switux/AstroWeatherStation/pictures/SQM + CloudCover sensors _1 of 2.JPG

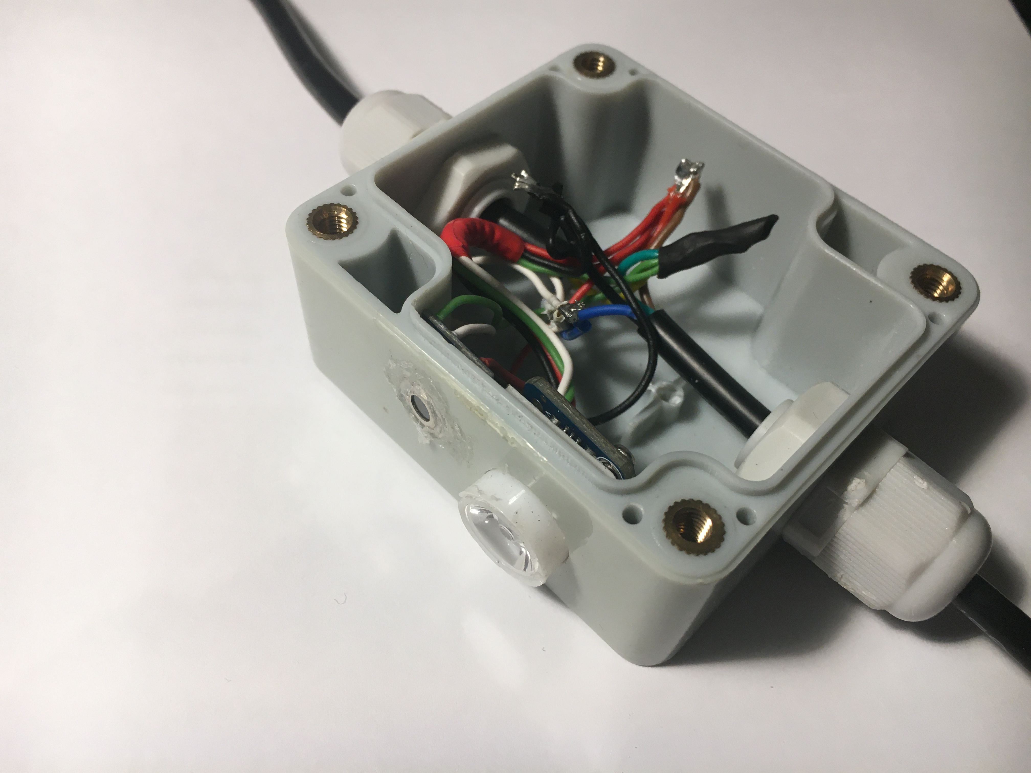
pictures/SQM + CloudCover sensors _1 of 2.JPG
