switux/AstroWeatherStation/pictures/SQM + CloudCover sensors _2 of 2.JPG

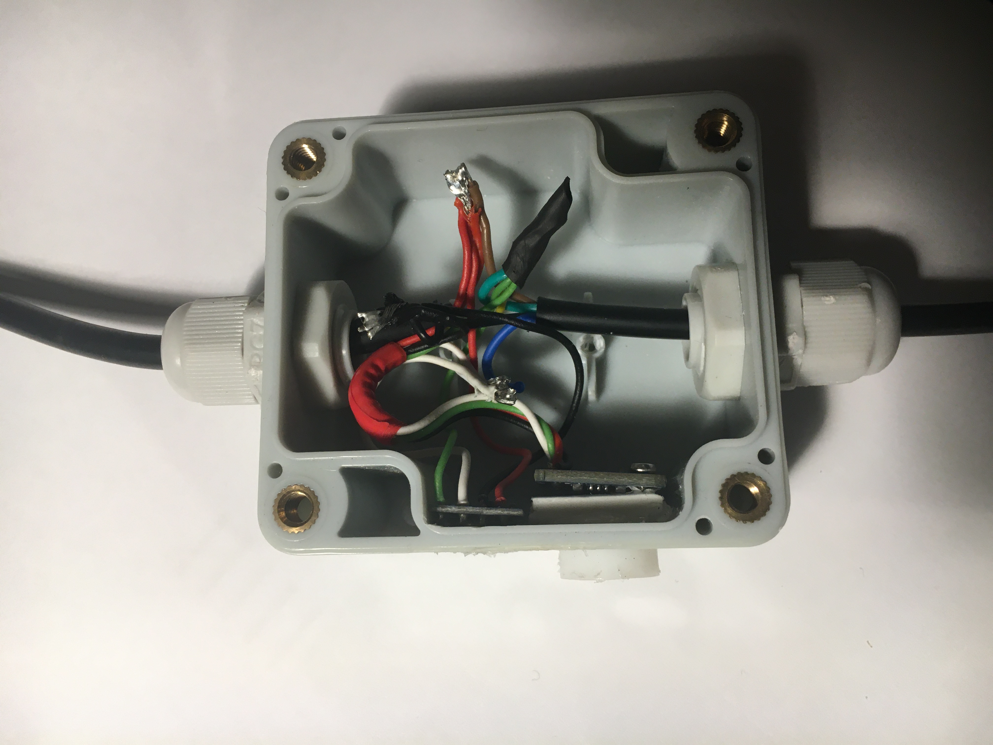
pictures/SQM + CloudCover sensors _2 of 2.JPG
