switux/AstroWeatherStation/schematics/AWS_12V_3.0.0_bb.png

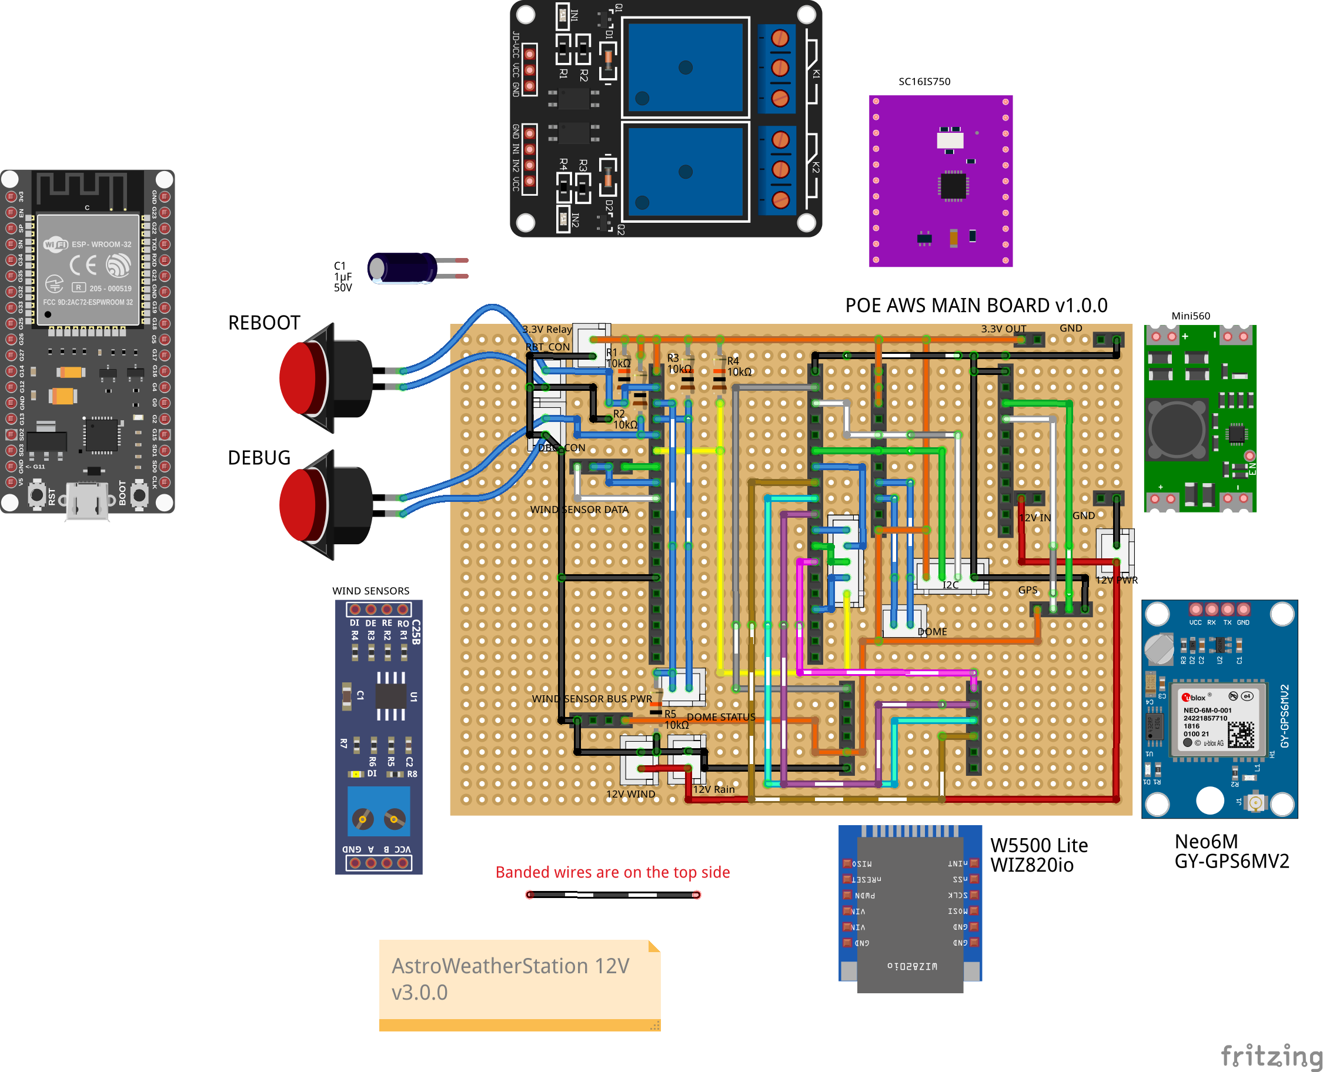
schematics/AWS_12V_3.0.0_bb.png
