switux/AstroWeatherStation/schematics/AWS_12V_3.0.0_pcb.png

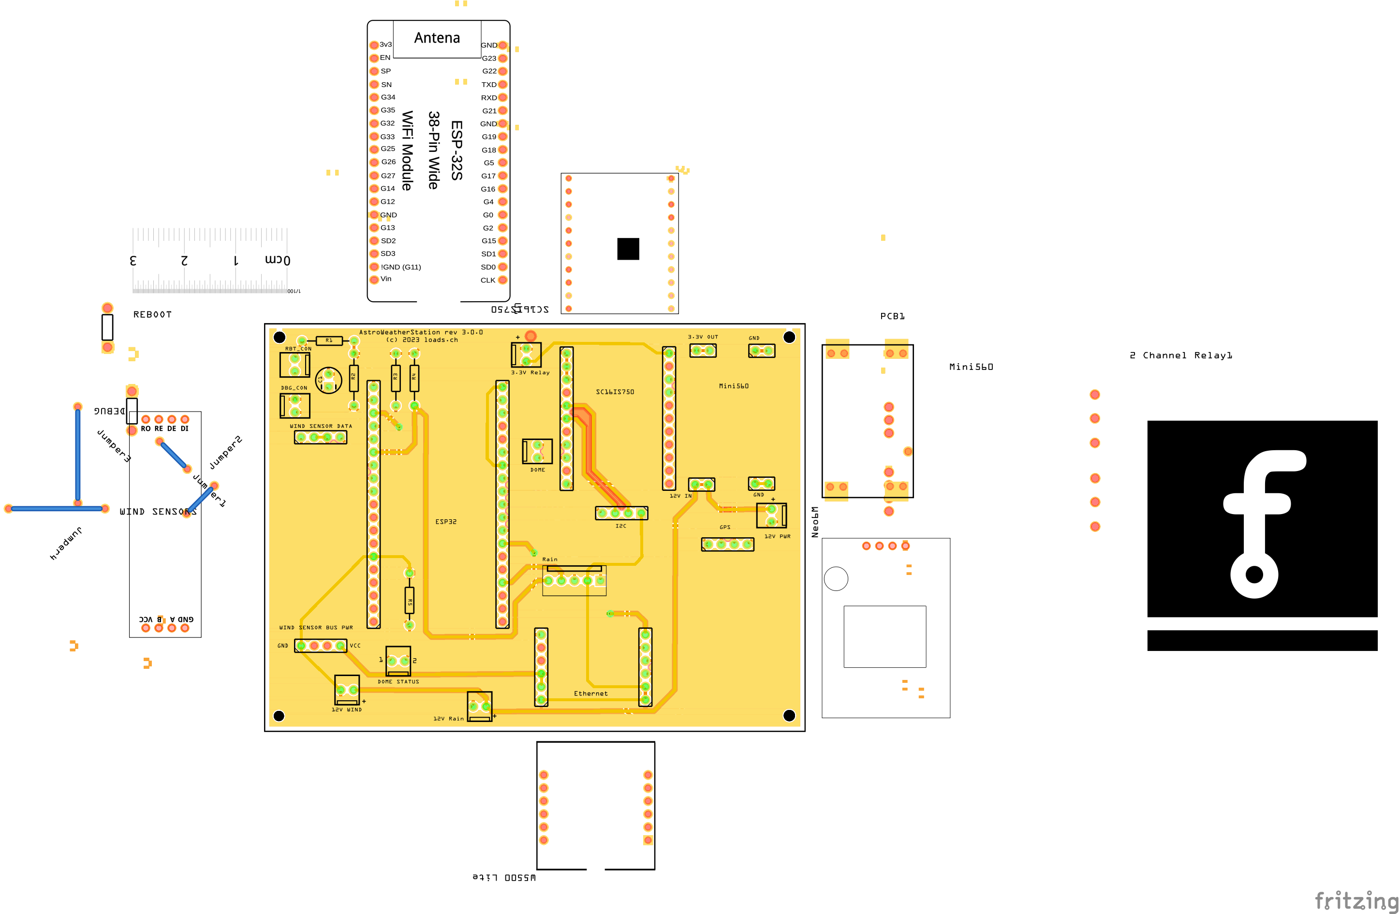
schematics/AWS_12V_3.0.0_pcb.png
