switux/AstroWeatherStation/schematics/perfboard_bottom_view.jpg

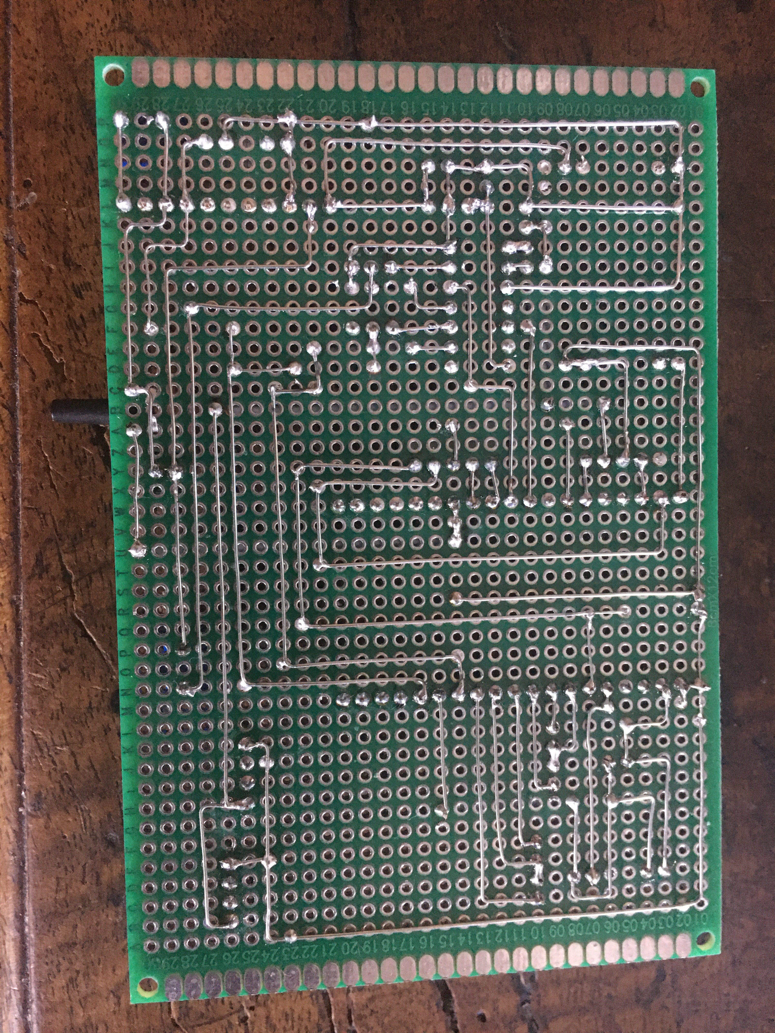
schematics/perfboard_bottom_view.jpg
