switux/AstroWeatherStation/src/AWSNetwork.cpp

/*
	AstroWeatherStation.cpp

	(c) 2023-2024 F.Lesage

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
	You should have received a copy of the GNU General Public License along
	with this program. If not, see <https://www.gnu.org/licenses/>.
*/

#include <Ethernet.h>
#include <SSLClient.h>
#include <AsyncUDP_ESP32_W5500.h>
#include <ESPAsyncWebServer.h>
#include <WiFi.h>
#include <WiFiClient.h>
#include <HTTPClient.h>
#include "Embedded_Template_Library.h"
#include "etl/string.h"

#include "common.h"
#include "config_manager.h"
#include "gpio_config.h"
#include "AWSNetwork.h"
#include "AstroWeatherStation.h"

extern AstroWeatherStation station;

AWSNetwork::AWSNetwork( void )
{
	ssl_eth_client = nullptr;
	current_wifi_mode = aws_wifi_mode::sta;
	current_pref_iface = aws_iface::wifi_sta;
	memset( wifi_mac, 0, 6 );
}

IPAddress AWSNetwork::cidr_to_mask( byte cidr )
{
	uint32_t		subnet;

	if ( cidr )
		subnet = htonl( ~(( 1 << ( 32 - cidr )) -1 ) );
	else
		subnet = htonl( 0 );

	return IPAddress( subnet );
}

bool AWSNetwork::connect_to_wifi()
{
	uint8_t		remaining_attempts	= 10;
	char		*ip = nullptr;
	char		*cidr = nullptr;
	const char	*ssid		= config->get_parameter<const char *>( "wifi_sta_ssid" );
	const char	*password	= config->get_parameter<const char *>( "wifi_sta_password" );
	char		*dummy;

	if (( WiFi.status () == WL_CONNECTED ) && !strcmp( ssid, WiFi.SSID().c_str() )) {

		if ( debug_mode )
			Serial.printf( "[NETWORK   ] [DEBUG] Already connected to SSID [%s].\n", ssid );
		return true;
	}

	Serial.printf( "[NETWORK   ] [INFO ] Attempting to connect to SSID [%s] ", ssid );

	if ( static_cast<aws_ip_mode>(config->get_parameter<int>( "wifi_sta_ip_mode" )) == aws_ip_mode::fixed ) {

		if ( etl::string_view( config->get_parameter<const char *>( "wifi_sta_ip" )).size() ) {

			etl::string<32> buf;
			strlcpy( buf.data(), config->get_parameter<const char *>( "wifi_sta_ip" ), buf.capacity() );
		 	ip = strtok_r( buf.data(), "/", &dummy );
		}
		if ( ip )
			cidr = strtok_r( nullptr, "/", &dummy );

  		wifi_sta_ip.fromString( ip );
  		wifi_sta_gw.fromString( config->get_parameter<const char *>( "wifi_sta_gw" ));
  		wifi_sta_dns.fromString( config->get_parameter<const char *>( "wifi_sta_dns" ));
		// flawfinder: ignore
  		wifi_sta_subnet = cidr_to_mask( static_cast<unsigned int>( atoi( cidr ) ));
		WiFi.config( wifi_sta_ip, wifi_sta_gw, wifi_sta_subnet, wifi_sta_dns );

	}
	WiFi.begin( ssid , password );

	while (( WiFi.status() != WL_CONNECTED ) && ( --remaining_attempts > 0 )) {	// NOSONAR

    Serial.print( "." );
		delay( 1000 );
	}

	if ( WiFi.status () == WL_CONNECTED ) {

		wifi_sta_ip = WiFi.localIP();
		wifi_sta_subnet = WiFi.subnetMask();
		wifi_sta_gw = WiFi.gatewayIP();
		wifi_sta_dns = WiFi.dnsIP();
		config->set_parameter( "run_wifi_sta_ip", wifi_sta_ip.toString().c_str() );
		config->set_parameter( "run_wifi_sta_subnet", wifi_sta_subnet.toString().c_str() );
		config->set_parameter( "run_wifi_sta_gw", wifi_sta_gw.toString().c_str() );
		Serial.printf( " OK. Using IP [%s]\n", WiFi.localIP().toString().c_str() );
		return true;
	}

	Serial.printf( "NOK.\n" );

	return false;
}

IPAddress AWSNetwork::get_gw( aws_iface iface )
{
	switch( iface ) {
		case aws_iface::wifi_ap:
			return wifi_ap_gw;
		case aws_iface::wifi_sta:
			return wifi_sta_gw;
		case aws_iface::eth:
			return eth_gw;
		default:
			return IPAddress( 0, 0, 0, 0 );
	}
}

IPAddress AWSNetwork::get_ip( aws_iface iface )
{
	switch( iface ) {
		case aws_iface::wifi_ap:
			return wifi_ap_ip;
		case aws_iface::wifi_sta:
			return wifi_sta_ip;
		case aws_iface::eth:
			return eth_ip;
		default:
			return IPAddress( 0, 0, 0, 0 );
	}
}

IPAddress AWSNetwork::get_subnet( aws_iface iface )
{
	switch( iface ) {
		case aws_iface::wifi_ap:
			return wifi_ap_subnet;
		case aws_iface::wifi_sta:
			return wifi_sta_subnet;
		case aws_iface::eth:
			return eth_subnet;
		default:
			return IPAddress( 0, 0, 0, 0 );
	}
}
uint8_t *AWSNetwork::get_wifi_mac( void )
{
	return wifi_mac;
}

bool AWSNetwork::initialise_ethernet( void )
{
	char					*ip		= nullptr;
	char					*cidr	= nullptr;
	char					*dummy;
	std::array<uint8_t,6>	eth_mac	= config->get_eth_mac();

	pinMode( 4, OUTPUT );
	digitalWrite( 4, HIGH );
	delay( 250 );
	digitalWrite( 4, LOW );
	delay( 50 );
	digitalWrite( 4, HIGH );
	delay( 350 );

	ESP32_W5500_onEvent();

	// You will have to change esp_w5500.cpp ETH.begin() to make it accept eth_mac even if a mac already exists,
	// honestly I do not understand why you would silently override the eth_mac parameter
	if ( !ETH.begin( GPIO_SPI_MISO, GPIO_SPI_MOSI, GPIO_SPI_SCK, GPIO_SPI_CS_ETH, GPIO_SPI_INT, SPI_CLOCK_MHZ, SPI3_HOST, eth_mac.data() )) {

		Serial.printf( "[NETWORK   ] [ERROR] Could not initialise ethernet!\n" );
		return false;
	}

  	if ( static_cast<aws_ip_mode>( config->get_parameter<int>( "eth_ip_mode" )) == aws_ip_mode::fixed ) {

		if ( etl::string_view( config->get_parameter<const char *>( "eth_ip" )).size() ) {

			etl::string<32> buf;
			strlcpy( buf.data(), config->get_parameter<const char *>( "eth_ip" ), buf.capacity() );
		 	ip = strtok_r( buf.data(), "/", &dummy );
		}
		if ( ip )
			cidr = strtok_r( nullptr, "/", &dummy );

  		eth_ip.fromString( ip );
  		eth_gw.fromString( config->get_parameter<const char *>( "eth_gw" ));
  		eth_dns.fromString( config->get_parameter<const char *>( "eth_dns" ));
		// flawfinder: ignore
		ETH.config( eth_ip, eth_gw, cidr_to_mask( static_cast<unsigned int>( atoi( cidr )) ), eth_dns );
  	}

	ESP32_W5500_waitForConnect();

	eth_ip = ETH.localIP();
	eth_gw = ETH.gatewayIP();
	eth_subnet = ETH.subnetMask();
	eth_dns = ETH.dnsIP();

	config->set_parameter( "run_eth_ip", eth_ip.toString().c_str() );
	config->set_parameter( "run_eth_subnet", eth_subnet.toString().c_str() );
	config->set_parameter( "run_eth_gw", eth_gw.toString().c_str() );
		
	return true;
}

bool AWSNetwork::initialise( AWSConfig *_config, bool _debug_mode )
{
	debug_mode = _debug_mode;
	config = _config;

	esp_read_mac( wifi_mac, ESP_MAC_WIFI_STA );

	switch ( static_cast<aws_iface>( config->get_parameter<int>( "pref_iface" )) ) {

		case aws_iface::wifi_ap:
		case aws_iface::wifi_sta:
			return initialise_wifi();

		case aws_iface::eth:
			return initialise_ethernet();

		default:
			Serial.printf( "[NETWORK   ] [ERROR] Invalid preferred iface, falling back to WiFi.\n" );
			initialise_wifi();

	}
	return false;
}

bool AWSNetwork::initialise_wifi( void )
{
	switch ( static_cast<aws_wifi_mode>( config->get_parameter<int>( "wifi_mode" )) ) {

		case aws_wifi_mode::ap:
			if ( debug_mode )
				Serial.printf( "[NETWORK   ] [DEBUG] Booting in AP mode.\n" );
			WiFi.mode( WIFI_AP );
			return start_hotspot();

		case aws_wifi_mode::both:
			if ( debug_mode )
				Serial.printf( "[NETWORK   ] [DEBUG] Booting in AP+STA mode.\n" );
			WiFi.mode( WIFI_AP_STA );
			return ( start_hotspot() && connect_to_wifi() );

		case aws_wifi_mode::sta:
			if ( debug_mode )
				Serial.printf( "[NETWORK   ] [DEBUG] Booting in STA mode.\n" );
			WiFi.mode( WIFI_STA );
			return connect_to_wifi();

		default:
			Serial.printf( "[NETWORK   ] [ERROR] Unknown wifi mode [%d]\n",  config->get_parameter<int>( "wifi_mode" ) );
	}
	return false;
}

byte AWSNetwork::mask_to_cidr( uint32_t subnet )
{
	byte		cidr 	= 0;
	uint32_t	mask 	= 0x80000000;
	uint32_t	x 		= ntohl( subnet );

	while ( mask != 0 ) {
		if (( x & mask ) != mask )
			break;
		cidr++;
		mask >>= 1;
	}
	return cidr;
}

bool AWSNetwork::eth_post_content( const char *remote_server, etl::string<128> &final_endpoint, const char *jsonString )
{
	HTTPClient 			http;
	uint8_t				http_code;

	if ( !http.begin( final_endpoint.data() )) {
	
		if ( debug_mode )
        	Serial.print( "NOK.\n" );
		return false;
		
	}

	if ( debug_mode )
    	Serial.print( "OK.\n" );

	http.setFollowRedirects( HTTPC_FORCE_FOLLOW_REDIRECTS );
	http.addHeader( "Content-Type", "application/json" );
	http_code = http.POST( jsonString );
	http.end();
	if ( http_code == 200 )
		return true;

	if ( debug_mode )
		Serial.printf( "[NETWORK   ] [DEBUG] HTTP response: %d\n", http_code );

	return false;
}

bool AWSNetwork::wifi_post_content( const char *remote_server, etl::string<128> &final_endpoint, const char *jsonString )
{
	HTTPClient 			http;
	uint8_t				http_code;
	WiFiClientSecure	wifi_client;

	wifi_client.setCACert( config->get_root_ca().data() );
	if ( !wifi_client.connect( remote_server, 443 )) {

		if ( debug_mode )
        	Serial.printf( "NOK.\n" );
		return false;
	}

	if ( debug_mode )
    	Serial.printf( "OK.\n" );

	http.begin( wifi_client, final_endpoint.data() );
	http.setFollowRedirects( HTTPC_FORCE_FOLLOW_REDIRECTS );
	http.addHeader( "Content-Type", "application/json" );
	http_code = http.POST( jsonString );
	http.end();
   	wifi_client.stop();

	if ( http_code == 200 )
		return true;
		
	if ( debug_mode )
		Serial.printf( "[NETWORK   ] [DEBUG] HTTP response: %d\n", http_code );

	return false;
}

bool AWSNetwork::post_content( const char *endpoint, size_t endpoint_len, const char *jsonString )
{
	uint8_t				fe_len;
	etl::string<128>	final_endpoint;
	int 				l;
	const char			*remote_server = config->get_parameter<const char *>( "remote_server" );
	etl::string<128>	url;
	uint8_t 			url_len = 8 + etl::string_view( config->get_parameter<const char *>( "remote_server" )).size() + 1 + etl::string_view( config->get_parameter<const char *>( "url_path" )).size() + 1;
	const char			*url_path = config->get_parameter<const char *>( "url_path" );

	if ( url_len > url.capacity() ) {

		etl::string<64> tmp;
		snprintf( tmp.data(), tmp.capacity(), "Content POST URL is too long (%d > %d)", url_len, url.capacity() );
		station.send_alarm( "[STATION] BUG", tmp.data() );
		Serial.printf( "[NETWORK   ] [BUG  ] URL is too long (%d > %d)\n", url_len, url.capacity() );
		return false;
	}

	url.assign( "https://" );
	url.append( remote_server );
	url.append( "/" );
	url.append( url_path );
	url.append( "/" );

	fe_len = l + endpoint_len + 2;
	if ( fe_len > final_endpoint.capacity() ) {

		etl::string<64> tmp;
		snprintf( tmp.data(), tmp.capacity(), "Content POST final endpoint is too long (%d > %d)", fe_len, final_endpoint.capacity() );
		station.send_alarm( "[STATION] BUG", tmp.data() );
		Serial.printf( "[NETWORK   ] [ERROR] Final endpoint is too long (%d > %d)\n", fe_len, final_endpoint.capacity() );
		return false;
	}

	final_endpoint.assign( url );
	final_endpoint.append( endpoint );

	if ( debug_mode )
		Serial.printf( "[NETWORK   ] [DEBUG] Connecting to server [%s:443] ...", remote_server );

	if ( static_cast<aws_iface>( config->get_parameter<int>( "pref_iface" )) == aws_iface::eth )
		return eth_post_content( remote_server, final_endpoint, jsonString );

	return wifi_post_content( remote_server, final_endpoint, jsonString );
}

bool AWSNetwork::start_hotspot( void )
{
	const char	*ssid		= config->get_parameter<const char *>( "wifi_ap_ssid" );
	const char	*password	= config->get_parameter<const char *>( "wifi_ap_password" );

	char *ip = nullptr;
	char *cidr = nullptr;
	char *dummy;

	if ( debug_mode )
		Serial.printf( "[NETWORK   ] [DEBUG] Trying to start AP on SSID [%s] with password [%s]\n", ssid, password );

	if ( WiFi.softAP( ssid, password )) {

		if ( etl::string_view( config->get_parameter<const char *>( "wifi_ap_ip" )).size() ) {

			etl::string<32> buf;
			strlcpy( buf.data(), config->get_parameter<const char *>( "wifi_ap_ip" ), buf.capacity() );
		 	ip = strtok_r( buf.data(), "/", &dummy );
		}
		if ( ip )
			cidr = strtok_r( nullptr, "/", &dummy );

  		wifi_ap_ip.fromString( ip );
  		wifi_ap_gw.fromString( config->get_parameter<const char *>( "wifi_ap_gw" ));
		// flawfinder: ignore
  		wifi_ap_subnet = cidr_to_mask( static_cast<unsigned int>( atoi( cidr )) );

		WiFi.softAPConfig( wifi_ap_ip, wifi_ap_gw, wifi_ap_subnet );
		Serial.printf( "[NETWORK   ] [INFO ] Started hotspot on SSID [%s/%s] and configuration server @ IP=%s/%s\n", ssid, password, ip, cidr );
		return true;
	}
	return false;
}

void AWSNetwork::webhook( const char *json_msg )
{
	// Placeholder for #155
	Serial.printf( "[STATION   ] [INFO ] Calling webhook [%s]\n", json_msg );
}
