switux/AstroWeatherStation/src/alpaca_device.cpp

/*
  	alpaca_device.cpp

	(c) 2023-2024 F.Lesage

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
	You should have received a copy of the GNU General Public License along
	with this program. If not, see <https://www.gnu.org/licenses/>.
*/

#include <AsyncUDP_ESP32_W5500.hpp>
#include <ESPAsyncWebServer.h>

#include "device.h"
#include "alpaca_device.h"

alpaca_device::alpaca_device( alpaca_interface_version_t intver ) : interfaceversion( intver )
{
}

bool alpaca_device::get_debug_mode( void )
{
	return debug_mode;
}

bool alpaca_device::get_is_connected( void )
{
	return is_connected;
}

const char *alpaca_device::has_parameter( AsyncWebServerRequest *request, char *name, bool case_sensitive )
{
	bool b = false;
	const char *s;

	for( int i = 0; ( i < request->args() ) && !b; i++ ) {

		if ( ( s = request->argName( i ).c_str() ) == nullptr )
			break;

		if ( ! ( b = ( case_sensitive ? !strcmp( name, s ) : !strcasecmp( name, s ))) )
			s = nullptr;
	}
	return s;
}

void alpaca_device::send_connected( AsyncWebServerRequest *request, etl::string<128> &transaction_details )
{
	etl::string<256>	message_str;
	snprintf( message_str.data(), message_str.capacity(), R"json({"ErrorNumber":0,"ErrorMessage":"","Value":%s,%s})json", is_connected?"true":"false", transaction_details.data() );
	request->send( 200, "application/json", static_cast<const char *>( message_str.data() ) );
}

void alpaca_device::not_implemented( AsyncWebServerRequest *request, etl::string<128> &transaction_details, const char *msg )
{
	etl::string<256>	message_str;
	snprintf( message_str.data(), message_str.capacity(), R"json({%s,"ErrorNumber":1024,"ErrorMessage":"%s"})json", transaction_details.data(), msg?msg:"" );
	request->send( 200, "application/json", static_cast<const char *>( message_str.data() ) );
}

void alpaca_device::device_error( AsyncWebServerRequest *request, etl::string<128> &transaction_details, ascom_driver_error error, char *msg )
{
	etl::string<256>	message_str;
	if ( is_connected )
		snprintf( message_str.data(), message_str.capacity(), R"json({"ErrorNumber":%d,"ErrorMessage":"%s","Value":false,%s})json", 0x500 + static_cast<byte>( error ), msg, transaction_details.data() );
	else
		snprintf( message_str.data(), message_str.capacity(), R"json({"ErrorNumber":1031,"ErrorMessage":"Device is not connected",%s})json", transaction_details.data() );

	request->send( 200, "application/json", static_cast<const char *>( message_str.data() ) );
}

void alpaca_device::send_value( AsyncWebServerRequest *request, etl::string<128> &transaction_details, bool truefalse )
{
	etl::string<256>	message_str;
	if ( is_connected )
		snprintf( message_str.data(), message_str.capacity(), R"json({"ErrorNumber":0,"ErrorMessage":"","Value":%s,%s})json", truefalse?"true":"false", transaction_details.data() );
	else
		snprintf( message_str.data(), message_str.capacity(), R"json({"ErrorNumber":1031,"ErrorMessage":"Device is not connected",%s})json", transaction_details.data() );

	request->send( 200, "application/json", static_cast<const char *>( message_str.data() ) );

}

void alpaca_device::send_value( AsyncWebServerRequest *request, etl::string<128> &transaction_details, float value )
{
	etl::string<256>	message_str;
	if ( is_connected )
		snprintf( message_str.data(), message_str.capacity(), R"json({"ErrorNumber":0,"ErrorMessage":"","Value":%f,%s})json", value, transaction_details.data() );
	else
		snprintf( message_str.data(), message_str.capacity(), R"json({"ErrorNumber":1031,"ErrorMessage":"Device is not connected",%s})json", transaction_details.data() );

	request->send( 200, "application/json", static_cast<const char *>( message_str.data() ) );

}

void alpaca_device::send_value( AsyncWebServerRequest *request, etl::string<128> &transaction_details, byte value )
{
	etl::string<256>	message_str;
	if ( is_connected )
		snprintf( message_str.data(), message_str.capacity(), R"json({"ErrorNumber":0,"ErrorMessage":"","Value":%d,%s})json", value, transaction_details.data() );
	else
		snprintf( message_str.data(), message_str.capacity(), R"json({"ErrorNumber":1031,"ErrorMessage":"Device is not connected",%s})json", transaction_details.data() );

	request->send( 200, "application/json", static_cast<const char *>( message_str.data() ) );

}

bool alpaca_device::send_description( AsyncWebServerRequest *request, etl::string<128> &transaction_details )
{
	if ( request->method() != HTTP_GET )
		return false;

	etl::string<256>	message_str;
	snprintf( message_str.data(), message_str.capacity(), R"json({"ErrorNumber":0,"ErrorMessage":"","Value":"%s",%s})json", description, transaction_details.data() );
	request->send( 200, "application/json", static_cast<const char *>( message_str.data() ) );
	return true;
}

bool alpaca_device::send_driverinfo( AsyncWebServerRequest *request, etl::string<128> &transaction_details )
{
	if ( request->method() != HTTP_GET )
		return false;

	etl::string<256>	message_str;
	snprintf( message_str.data(), message_str.capacity(), R"json({"ErrorNumber":0,"ErrorMessage":"","Value":"%s",%s})json", driverinfo, transaction_details.data() );
	request->send( 200, "application/json", static_cast<const char *>( message_str.data() ) );
	return true;
}

bool alpaca_device::send_driverversion( AsyncWebServerRequest *request, etl::string<128> &transaction_details )
{
	if ( request->method() != HTTP_GET )
		return false;

	etl::string<256>	message_str;
	snprintf( message_str.data(), message_str.capacity(), R"json({"ErrorNumber":0,"ErrorMessage":"","Value":"%s",%s})json", driverversion, transaction_details.data() );
	request->send( 200, "application/json", static_cast<const char *>( message_str.data() ) );
	return true;
}

bool alpaca_device::send_interfaceversion( AsyncWebServerRequest *request, etl::string<128> &transaction_details )
{
	if ( request->method() != HTTP_GET )
		return false;

	etl::string<256>	message_str;
	snprintf( message_str.data(), message_str.capacity(), R"json({"ErrorNumber":0,"ErrorMessage":"","Value":%d,%s})json", interfaceversion, transaction_details.data() );
	request->send( 200, "application/json", static_cast<const char *>( message_str.data() ) );
	return true;
}

bool alpaca_device::send_name( AsyncWebServerRequest *request, etl::string<128> &transaction_details )
{
	if ( request->method() != HTTP_GET )
		return false;

	etl::string<256>	message_str;
	snprintf( message_str.data(), message_str.capacity(), R"json({"ErrorNumber":0,"ErrorMessage":"","Value":"%s",%s})json", name, transaction_details.data() );
	request->send( 200, "application/json", static_cast<const char *>( message_str.data() ) );
	return true;
}

bool alpaca_device::send_supportedactions( AsyncWebServerRequest *request, etl::string<128> &transaction_details )
{
	if ( request->method() != HTTP_GET )
		return false;

	etl::string<256>	message_str;
	if ( is_connected )
		snprintf( message_str.data(), message_str.capacity(), R"json({"ErrorNumber":0,"ErrorMessage":"","Value":%s,%s})json", supportedactions.data(), transaction_details.data() );
	else
		snprintf( message_str.data(), message_str.capacity(), R"json({"ErrorNumber":1031,"ErrorMessage":"Device is not connected",%s})json", transaction_details.data() );

	Serial.printf("ACTIONS: [%s] [%s]\n", message_str.data(), supportedactions.data() );
	
	request->send( 200, "application/json", static_cast<const char*>( message_str.data() ));
	return true;
}

void alpaca_device::set_debug_mode( bool b )
{
	debug_mode = b;
}

void alpaca_device::set_is_connected( bool b )
{
	is_connected = b;
}
