switux/AstroWeatherStation/src/AWSOTA.cpp

/*
  	AWSOTA.cpp

	(c) 2024 F.Lesage and inspired from ESP32-OTA-Pull by M.Hart

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
	You should have received a copy of the GNU General Public License along
	with this program. If not, see <https://www.gnu.org/licenses/>.
*/

#include <esp_task_wdt.h>
#include <AsyncUDP_ESP32_W5500.hpp>
#include <ESPAsyncWebServer.h>
#include <HTTPClient.h>
#include <Update.h>
#include <WiFi.h>

#include "Embedded_Template_Library.h"
#include "etl/string.h"

#include "common.h"
#include "AstroWeatherStation.h"
#include "AWSOTA.h"

extern bool	ota_update_ongoing;			// NOSONAR
extern AstroWeatherStation	station;

ota_status_t AWSOTA::check_for_update( const char *url, const char *root_ca, etl::string<26> &current_version, ota_action_t action = ota_action_t::CHECK_ONLY) {

	ota_status_t ota_status;

	if ( !download_json( url, root_ca )) {

		ota_status = ota_status_t::HTTP_FAILED;
		goto exit;
	}

	if (!aws_board_id.size() || !aws_config.size() || !aws_device_id.size()) {

		ota_status = ota_status_t::CONFIG_ERROR;
		goto exit;
	}

	for (auto ota_config : json_ota_config["Configurations"].as<JsonArray>()) {

		if (is_profile_match(ota_config, current_version)) {

			ota_status = handle_action(ota_config, root_ca, action);
			break;
		}
    }

	ota_status = ota_status_t::NO_UPDATE_PROFILE_FOUND;

exit:
	Serial.printf( "[OTA       ] [INFO ] Firmware OTA update result: (%d) %s.\n", ota_status, OTA_message( ota_status ));
	return ota_status;
}

bool AWSOTA::is_profile_match( const JsonObject &ota_config, const etl::string<26> &current_version )
{
	etl::string<32> board;
	etl::string<32>	device;
	etl::string<32>	config;
	etl::string<32> version;

    if ( ota_config["Board"].is<JsonVariant>() )
        board.assign( ota_config["Board"].as<const char *>() );

    if ( ota_config["Device"].is<JsonVariant>() )
		device.assign( ota_config["Device"].as<const char *>() );

    if ( ota_config["Config"].is<JsonVariant>() )
		config.assign( ota_config["Config"].as<const char *>() );

    if ( ota_config["Version"].is<JsonVariant>() )
		version.assign( ota_config["Version"].as<const char *>() );

    return ( !board.size() || (board == aws_board_id) ) &&
           ( !device.size() || (device == aws_device_id) ) &&
           ( !config.size() || (config == aws_config) ) &&
           ( !version.size() || (version > current_version) );
}

ota_status_t AWSOTA::handle_action( const JsonObject &ota_config, const char *root_ca, ota_action_t action )
{
	if ( action == ota_action_t::CHECK_ONLY )
		return ota_status_t::UPDATE_AVAILABLE;

    if ( action == ota_action_t::UPDATE_AND_BOOT ) {

		ota_update_ongoing = true;
		save_firmware_sha256(ota_config["SHA256"].as<const char *>());
	}

	if ( !do_ota_update( ota_config["URL"], root_ca, action ))
		return ota_status_t::OTA_UPDATE_FAIL;

	return ota_status_t::UPDATE_OK;
}

bool AWSOTA::do_ota_update( const char *url, const char *root_ca, ota_action_t action )
{
	HTTPClient	http;
	
	if ( !http.begin( url, root_ca )) {

		status_code = ota_status_t::HTTP_FAILED;
		return false;

	}

	http_status = http.GET();

	if ( http_status != 200 ) {

		http.end();
		return false;
	}

	int total_length = http.getSize();

	if ( !Update.begin( UPDATE_SIZE_UNKNOWN )) {

		http.end();
		status_code = ota_status_t::OTA_UPDATE_FAIL;
		return false;
	}

	std::array<uint8_t,1280>	buffer;

	WiFiClient *stream = http.getStreamPtr();

	int offset = 0;
	while ( http.connected() && offset < total_length ) {

		size_t	bytes_available = stream->available();
		if ( bytes_available > 0 ) {

			size_t bytes_to_read = min( bytes_available, buffer.max_size() );
			size_t bytes_read = stream->readBytes( buffer.data(), bytes_to_read );
			esp_task_wdt_reset();
			size_t bytes_written = Update.write( buffer.data(), bytes_read );
			if ( bytes_read != bytes_written )
				break;
			offset += bytes_written;
			if ( progress_callback != nullptr )
				progress_callback( offset, total_length );
		}
		esp_task_wdt_reset();
	}

	esp_task_wdt_reset();
	http.end();
	esp_task_wdt_reset();

	if ( offset == total_length ) {

		Update.end( true );
		esp_task_wdt_reset();
		delay( 1000 );
		if ( action == ota_action_t::UPDATE_ONLY ) {

			status_code = ota_status_t::UPDATE_OK;
			return true;
		}
		ESP.restart();
	}
	
	status_code = ota_status_t::WRITE_ERROR;
	return false;
}

bool AWSOTA::download_json( const char *url, const char *root_ca )
{
	HTTPClient	http;

	if ( !http.begin( url, root_ca )) {

		status_code = ota_status_t::HTTP_FAILED;
		return false;
	}
	
	if ( ( http_status = http.GET()) == 200 )
		deserialisation_status = deserializeJson( json_ota_config, http.getString() );

	http.end();
	return (( http_status == 200 ) && ( deserialisation_status == DeserializationError::Ok ));
}

const char *AWSOTA::OTA_message( ota_status_t code )
{
	switch ( code ) {

		case ota_status_t::UPDATE_AVAILABLE:
			return "An update is available but wasn't installed";

		case ota_status_t::NO_UPDATE_PROFILE_FOUND:
			return "No profile matches";

		case ota_status_t::NO_UPDATE_AVAILABLE:
			return "Profile matched, but update not applicable";

		case ota_status_t::UPDATE_OK:
			return "An update was done, but no reboot";

		case ota_status_t::HTTP_FAILED:
			return "HTTP GET failure";

		case ota_status_t::WRITE_ERROR:
			return "Write error";

		case ota_status_t::JSON_PROBLEM:
			return "Invalid JSON";

		case ota_status_t::OTA_UPDATE_FAIL:
			return "Update failure (no OTA partition?)";

		case ota_status_t::CONFIG_ERROR:
			return "OTA config has a problem";

		case ota_status_t::UNKNOWN:
			return "Undefined status";

	}
	return "Unhandled OTA status code";
}

void AWSOTA::save_firmware_sha256( const char *sha256 )
{
	Preferences nvs;
	if ( !nvs.begin( "firmware", false )) {

		Serial.printf( "[OTA       ] [ERROR] Could not open firmware NVS.\n" );
		station.send_alarm( "[Station] OTA NVS", "Could not open firmware NVS to save sha256" );
		return;
	}

	if ( nvs.putString( "sha256", sha256 ) ) {

		nvs.end();
		return;
	}

	nvs.end();
	Serial.printf( "[OTA       ] [ERROR] Could not save firmware SHA256 on NVS.\n" );
	station.send_alarm( "[Station] OTA NVS", "Could not save firmware SHA256 on NVS" );
}

void AWSOTA::set_aws_board_id( etl::string<24> &board )
{
	aws_board_id = etl::string_view( board.data() );
}

void AWSOTA::set_progress_callback( std::function<void(int, int)> callback )
{
	progress_callback = callback;
}

void AWSOTA::set_aws_config( etl::string<32> &config )
{
	aws_config = etl::string_view( config.data() );
}

void AWSOTA::set_aws_device_id( etl::string<18> &device )
{
	aws_device_id = etl::string_view( device.data() );
}
