switux/AstroWeatherStation/src/dome.cpp

/*
  	dome.cpp

	(c) 2023-2024 F.Lesage

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
	You should have received a copy of the GNU General Public License along
	with this program. If not, see <https://www.gnu.org/licenses/>.
*/

#include <Arduino.h>
#include <esp_task_wdt.h>
#include <AsyncUDP_ESP32_W5500.hpp>
#include <ESPAsyncWebServer.h>

#include "gpio_config.h"
#include "common.h"
#include "SC16IS750.h"
#include "device.h"
#include "dome.h"
#include "AstroWeatherStation.h"

extern void IRAM_ATTR		_handle_dome_shutter_open_change( void );
extern void IRAM_ATTR		_handle_dome_shutter_closed_change( void );

extern AstroWeatherStation	station;
extern time_t 				last_ntp_time;		// NOSONAR
extern uint16_t				ntp_time_misses;	// NOSONAR

//
// IMPORTANT: Some indications about dome shutter status handling by this driver
//
//	==> There are 3 pins to control and monitor the dome shutter
//
//		Control: two independant shutter closure systems can be attached, for redundancy, and they are connected to a pull-down resistor (the relay will trigger when the signal is down)
//				GPIO_DOME_1 if a SC16IS750 GPIO extender is used
//				GPIO_DOME_1_DIRECT if not
//
//				The DOME SHUTTER will be kept OPEN if and only if the pin level is HIGH
//					==> if the station or the pin is DOWN, the dome will be CLOSED no matter what.
//
//		Status:
//				GPIO_DOME_CLOSED, connected to a pull-down resistor
//						if pin level is DOWN, the dome shutter is not expected to be CLOSED (could be closing or opening)
//							==> it requires an active action (pulling HIGH the pin level) to indicate that the shutter is CLOSED
//				GPIO_DOME_OPEN, connected to a pull-down resistor 
//						if pin level is DOWN, the dome shutter is not expected to be OPEN (could be closing or opening)
//							==> it requires an active action (pulling HIGH the pin level) to indicate that the shutter is OPEN
//

Dome::Dome( void )
{
	set_name( "Roll-off roof" );
	set_description( "Generic relay driven roll-off roof" );
	set_driver_version( "1.0" );
}

bool Dome::get_shutter_closed_status( void )
{
	if ( !is_connected ) {

		Serial.printf( "[DOME      ] [ERROR] Dome is not initialised, cannot get shutter closed status!\n" );
		return false;
	}

	bool closed_shutter = ( digitalRead( GPIO_DOME_CLOSED ) == HIGH );
	bool open_shutter = ( digitalRead( GPIO_DOME_OPEN ) == HIGH );

	if ( closed_shutter ) {

		dome_data->shutter_status = dome_shutter_status_t::Closed;
		dome_data->closed_sensor = true;

	} else {

		if ( open_shutter )
			dome_data->shutter_status = dome_shutter_status_t::Open;

		else {

			if ( dome_data->shutter_status == dome_shutter_status_t::Closed )
				dome_data->shutter_status = dome_shutter_status_t::Opening;

		}
		dome_data->closed_sensor = false;

	}

	if ( get_debug_mode() )
		Serial.printf( "[DOME      ] [DEBUG] Dome shutter closed : %s\n", closed_shutter ? "yes" : "no" );

	return closed_shutter;
}

bool Dome::get_shutter_open_status( void )
{
	if ( !is_connected ) {

		Serial.printf( "[DOME      ] [ERROR] Dome is not initialised, cannot get shutter open status!\n" );
		return false;
	}

	bool closed_shutter = ( digitalRead( GPIO_DOME_CLOSED ) == HIGH );
	bool open_shutter = ( digitalRead( GPIO_DOME_OPEN ) == HIGH );

	if ( open_shutter ) {

		dome_data->shutter_status = dome_shutter_status_t::Open;
		dome_data->open_sensor = true;

	} else {

		if ( closed_shutter )
			dome_data->shutter_status = dome_shutter_status_t::Closed;

		else {

			if ( dome_data->shutter_status == dome_shutter_status_t::Open )
				dome_data->shutter_status = dome_shutter_status_t::Closing;

		}
		dome_data->open_sensor = false;

	}

	if ( get_debug_mode() )
		Serial.printf( "[DOME      ] [DEBUG] Dome shutter open : %s\n", open_shutter ? "yes" : "no" );

	return open_shutter;
}

bool Dome::close_shutter( void )
{
	if ( !is_connected ) {

		Serial.printf( "[DOME      ] [ERROR] Dome is not initialised, cannot close shutter!\n" );
		return false;
	}

	dome_data->close_command = true;

	if ( sc16is750 ) {

		while ( xSemaphoreTake( i2c_mutex, 50 / portTICK_PERIOD_MS ) != pdTRUE );

		sc16is750->digitalWrite( GPIO_DOME_1, LOW );

		xSemaphoreGive( i2c_mutex );

	} else

		digitalWrite( GPIO_DOME_1_DIRECT, LOW );

	do_close_shutter = false;
	return true;
}

void Dome::control_task( void *dummy )	// NOSONAR
{
	while ( true ) {

			if ( do_close_shutter )
				close_shutter();
			else {
				if ( do_open_shutter )
					open_shutter();
			}

			delay( 1000 );
			get_shutter_closed_status();
			get_shutter_open_status();
	}
}

void Dome::initialise( dome_data_t *_dome_data, bool _debug_mode )
{
	set_debug_mode( _debug_mode );
	dome_data = _dome_data;

	if ( sc16is750 ) {

		pinMode( GPIO_DOME_1, OUTPUT );
		digitalWrite( GPIO_DOME_1, HIGH );

	} else {

		pinMode( GPIO_DOME_1_DIRECT, OUTPUT );
		digitalWrite( GPIO_DOME_1_DIRECT, HIGH );
	}

	pinMode( GPIO_DOME_OPEN, INPUT );
	pinMode( GPIO_DOME_CLOSED, INPUT );

	if ( get_shutter_closed_status() )
		dome_data->shutter_status = shutter_status = dome_shutter_status_t::Closed;
	else
		if ( get_shutter_open_status() )
			dome_data->shutter_status = shutter_status = dome_shutter_status_t::Open;
		else
			dome_data->shutter_status = shutter_status = dome_shutter_status_t::Opening;	// This is a convention
		
	dome_data->open_sensor = digitalRead( GPIO_DOME_OPEN );
	dome_data->closed_sensor = digitalRead( GPIO_DOME_CLOSED );
	dome_data->close_command = false;

	attachInterrupt( GPIO_DOME_CLOSED, _handle_dome_shutter_closed_change, CHANGE );
	attachInterrupt( GPIO_DOME_OPEN, _handle_dome_shutter_open_change, RISING );

	std::function<void(void *)> _control = std::bind( &Dome::control_task, this, std::placeholders::_1 );
	if ( xTaskCreatePinnedToCore(
		[](void *param) {	// NOSONAR
            std::function<void(void*)>* control_proxy = static_cast<std::function<void(void*)>*>( param );
            (*control_proxy)( NULL );
		}, "DomeControl", 2000, &_control, configMAX_PRIORITIES - 2, &dome_task_handle, 1 ) != pdPASS )
		Serial.printf( "[DOME      ] [ERROR] Could not start task [DomeControlTask]\n" );


	is_connected = true;
}

void Dome::initialise( I2C_SC16IS750 *_sc16is750, SemaphoreHandle_t _i2c_mutex, dome_data_t *_dome_data, bool _debug_mode )
{
	i2c_mutex =_i2c_mutex;
	sc16is750 = _sc16is750;
	initialise( _dome_data, _debug_mode );
}

bool Dome::open_shutter( void )
{
	if ( !is_connected ) {

		Serial.printf( "[DOME      ] [ERROR] Dome is not initialised, cannot open shutter!\n" );
		return false;
	}

	dome_data->close_command = close_shutter_command = do_close_shutter = false;
	do_open_shutter = false;

	if ( sc16is750 ) {

		while ( xSemaphoreTake( i2c_mutex, 50 / portTICK_PERIOD_MS ) != pdTRUE );

		sc16is750->digitalWrite( GPIO_DOME_1, HIGH );

		xSemaphoreGive( i2c_mutex );

	} else

		digitalWrite( GPIO_DOME_1_DIRECT, HIGH );

	return true;
}

void Dome::shutter_closed_change( void )
{
	if ( digitalRead( GPIO_DOME_CLOSED ))
		dome_data->shutter_status = shutter_status = dome_shutter_status_t::Closed;
	else
		dome_data->shutter_status = shutter_status = dome_shutter_status_t::Opening;
}

void Dome::shutter_open_change( void )
{
	if ( digitalRead( GPIO_DOME_OPEN ))
		dome_data->shutter_status = shutter_status = dome_shutter_status_t::Open;
	else
		dome_data->shutter_status = shutter_status = dome_shutter_status_t::Closing;
}

void Dome::trigger_close_shutter( void )
{
	close_shutter_command = do_close_shutter = true;
}
