switux/AstroWeatherStation/src/AWSGPS.cpp

/*
  	AWSGPS.cpp

	(c) 2023-2024 F.Lesage

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
	You should have received a copy of the GNU General Public License along
	with this program. If not, see <https://www.gnu.org/licenses/>.
*/

#include <stdint.h>
#include "defaults.h"
#include "gpio_config.h"
#include "AWSGPS.h"

const unsigned long	GPS_SPEED = 9600;

AWSGPS::AWSGPS( void )
{
	set_name( "GPS Receiver" );
	set_description( "" );
	set_driver_version( "1.0" );
}

void AWSGPS::read_GPS( void )
{
	unsigned long _start = millis();

	if ( sc16is750 ) {

		do {
			while( sc16is750->available() )
				// flawfinder: ignore
				gps.encode( sc16is750->read() );
			delay( 5 );
		} while( ( millis() - _start ) < 1000 );

	} else {

		do {
			while( gps_serial->available() )
				// flawfinder: ignore
				gps.encode( gps_serial->read() );
			delay( 5 );
		} while( ( millis() - _start ) < 1000 );
	}
}

void AWSGPS::feed( void *dummy )	// NOSONAR
{
	while( true ) {

		if ( sc16is750 ) {

			if ( xSemaphoreTake( i2c_mutex, 500 / portTICK_PERIOD_MS ) == pdTRUE ) {

				read_GPS();
				xSemaphoreGive( i2c_mutex );

			} else
				delay( 5000 );

		} else
			read_GPS();

		update_data();
		delay( 5000 );
	}
}

void AWSGPS::get_ublox_model( void )
{
    std::array<byte,10> ubx_nav_svinfo = { 0xB5, 0x62, 0x06, 0x30, 0x01, 0x00, 0x37, 0xE1, 0x74, 0x55 };

	for( const auto &b : ubx_nav_svinfo )
		gps_serial->write( b );

	delay( 1000 );

	for( int i = 0; i < 10; i++)
		while( gps_serial->available() ) {
			char c = gps_serial->read();
//			Serial.printf( "%c(%02x)", c, c );
		}
	return;
}

void AWSGPS::update_data( void )
{
	struct tm gpstime = {0};
	time_t now;

	gps_data->fix = gps.location.isValid();

	if ( gps_data->fix ) {

		gps_data->longitude = gps.location.lng();
		gps_data->latitude = gps.location.lat();
		gps_data->altitude = gps.altitude.meters();
		gpstime.tm_year = 	gps.date.year() - 1900;
		gpstime.tm_mon = gps.date.month() - 1;
		gpstime.tm_mday = gps.date.day();
		gpstime.tm_hour = gps.time.hour();
		gpstime.tm_min = gps.time.minute();
		gpstime.tm_sec = gps.time.second();
		gpstime.tm_isdst = -1;
		now = mktime( &gpstime );
		gps_data->time.tv_sec = now;
		if ( update_rtc )
			settimeofday( &gps_data->time, 0 );

	} else {

		gps_data->longitude = 0.F;
		gps_data->latitude = 0.F;
		gps_data->altitude = 0.F;
		now = mktime( &gpstime );
		gps_data->time.tv_sec = now;

	}
}

bool AWSGPS::initialise( gps_data_t *_gps_data, I2C_SC16IS750 *_sc16is750, SemaphoreHandle_t _i2c_mutex )
{
	gps_data = _gps_data;

	i2c_mutex = _i2c_mutex;
	while ( xSemaphoreTake( i2c_mutex, 500 / portTICK_PERIOD_MS ) != pdTRUE );
	sc16is750 = _sc16is750;

	if ( !sc16is750->begin( GPS_SPEED )) {

		Serial.printf( "[GPS       ] [ERROR] Could not find I2C UART. GPS disabled!\n" );
		xSemaphoreGive( i2c_mutex );
		return false;
	}
	get_ublox_model();
	xSemaphoreGive( i2c_mutex );
	return true;
}

bool AWSGPS::initialise( gps_data_t *_gps_data )
{
	gps_data = _gps_data;

	gps_serial = new HardwareSerial(2);
	gps_serial->begin( GPS_SPEED, SERIAL_8N1, GPS_RX, GPS_TX );
	if ( gps_serial->availableForWrite() ) {
		get_ublox_model();
		return true;
	}
	return false;
}

void AWSGPS::pilot_rtc( bool _update_rtc )
{
	update_rtc = _update_rtc;
}

void AWSGPS::resume( void )
{
	if ( gps_task_handle != NULL )
		vTaskResume( gps_task_handle );
}

bool AWSGPS::start( void )
{
	std::function<void(void *)> _feed = std::bind( &AWSGPS::feed, this, std::placeholders::_1 );
	if ( xTaskCreatePinnedToCore(
		[](void *param) {	// NOSONAR
            std::function<void(void*)>* feed_proxy = static_cast<std::function<void(void*)>*>( param );
            (*feed_proxy)( NULL );
		}, "GPS Feed Task", 2000, &_feed, 4, &gps_task_handle, 1 ) != pdPASS ) {

		Serial.printf( "[GPS       ] [ERROR] Could not start task [GPSFeed]\n" );
		return false;
	}

	return true;
}

void AWSGPS::suspend( void )
{
	if ( gps_task_handle != NULL )
		vTaskSuspend( gps_task_handle );
}

void AWSGPS::stop( void )
{
	if ( gps_task_handle != NULL )
		vTaskDelete( gps_task_handle );

	gps_task_handle = NULL;
}
