switux/AstroWeatherStation/src/alpaca_device.h

/*
	alpaca_device.h

	ASCOM ALPACA Server for the AstroWeatherStation (c) 2023-2024 F.Lesage

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
 */

#pragma once
#ifndef _ALPACA_DEVICE_H
#define _ALPACA_DEVICE_H

#include "Embedded_Template_Library.h"
#include "etl/string.h"

enum struct ascom_driver_error_t : byte
{
	NotAvailable,
	DeviceTimeout

};
using ascom_driver_error = ascom_driver_error_t;

using alpaca_device_description_t	= etl::string<68>;
using alpaca_driver_info_t			= etl::string<128>;
using alpaca_driver_version_t		= etl::string<3>;
using alpaca_device_name_t			= etl::string<64>;
using alpaca_supported_actions_t	= etl::string<128>;
using alpaca_interface_version_t	= int32_t;

class alpaca_device {

	private:

		bool						debug_mode			= false;
		bool						is_connected		= false;
		alpaca_device_description_t	description;
		alpaca_driver_info_t		driverinfo;
		alpaca_driver_version_t		driverversion;
		alpaca_device_name_t		name;
		alpaca_supported_actions_t	supportedactions	= "[]";
		alpaca_interface_version_t	interfaceversion	= 0;

	public:

		explicit 	alpaca_device( alpaca_interface_version_t );
		void		device_error( AsyncWebServerRequest *, etl::string<128> &, ascom_driver_error_t , char * );
		bool		get_debug_mode( void );
		bool		get_is_connected( void );
		const char	*has_parameter( AsyncWebServerRequest *, char *, bool );
		void		not_implemented( AsyncWebServerRequest *, etl::string<128> &, const char * );
		void		send_connected( AsyncWebServerRequest *, etl::string<128> & );
		bool		send_description( AsyncWebServerRequest *, etl::string<128> & );
		bool		send_driverinfo( AsyncWebServerRequest *, etl::string<128> & );
		bool		send_driverversion( AsyncWebServerRequest *, etl::string<128> & );
		bool		send_interfaceversion( AsyncWebServerRequest *, etl::string<128> & );
		bool		send_name( AsyncWebServerRequest *, etl::string<128> & );
		bool		send_supportedactions( AsyncWebServerRequest *, etl::string<128> & );
		void		send_value( AsyncWebServerRequest *, etl::string<128> &, bool );
		void		send_value( AsyncWebServerRequest *, etl::string<128> &, byte );
		void		send_value( AsyncWebServerRequest *, etl::string<128> &, float );
		void		set_debug_mode( bool );
		void		set_description( char * );
		void		set_device_name( char * );
		void		set_driver_info( char * );
		void		set_driver_version( char * );
		void		set_is_connected( bool );
		void		set_supported_actions( char * );

};

#endif
