switux/AstroWeatherStation/src/alpaca_server.h

/*
	alpaca_server.h

	ASCOM ALPACA Server for the AstroWeatherStation (c) 2023-2024 F.Lesage

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
 */

#pragma once
#ifndef _ALPACA_SERVER_H
#define _ALPACA_SERVER_H

#include "alpaca_dome.h"
#include "alpaca_safetymonitor.h"
#include "alpaca_observingconditions.h"
#include "alpaca_telescope.h"

const	uint16_t	ALPACA_SERVER_PORT	= 8080;

const uint8_t			CONFIGURED_DEVICES	= 4;
const etl::string<36>	AWS_UUID			= "ed0f1194-7cff-11ee-adf4-43fdf91ce20d";
const etl::string<36>	SAFETYMONITOR_UUID	= "be358e98-7cff-11ee-8804-93595b17357e";
const etl::string<36>	DOME_UUID			= "e3a90ace-7cff-11ee-b0f6-73db65e0b158";
const etl::string<36>	TELESCOPE_UUID		= "17e70650-8733-11ee-aa35-8f2796da5b48";

using configured_device_t = struct {

	etl::string<32>	DeviceName;
	etl::string<32>	DeviceType;
	uint32_t		DeviceNumber;
	etl::string<36>	UniqueID;

};

enum struct ascom_error_t : byte
{
	Ok,
	PropertyOrMethodNotImplemented,
	InvalidValue,
	ValueNotSet,
	NotConnected,
	InvalidWhileParked,
	InvalidWhileSlaved,
	InvalidOperation,
	ActionNotImplemented

};
using ascom_error = ascom_error_t;

class alpaca_server {

	public:

		explicit		alpaca_server( void );
		alpaca_server	*get_alpaca( void );
		bool			get_debug_mode( void );
		AsyncUDP		*get_discovery( void );
		void			loop( void );
		bool			start( IPAddress, bool );

	private:

		bool			bad_request		= false;
		bool			debug_mode		= false;
		bool			server_up		= false;

		AsyncWebServer 	*server			= nullptr;
		AsyncUDP		ascom_discovery;

		alpaca_dome					dome;
		alpaca_observingconditions	observing_conditions;
		alpaca_safetymonitor		safety_monitor;
		alpaca_telescope			telescope;

		ascom_error		transaction_status	= ascom_error_t::NotConnected;

		etl::string<255>	buf;
		// Issue #149
		etl::string<128>	transaction_details;

		int				client_id = 0;
		int				client_transaction_id = 0;
		int				server_transaction_id = 0;

		void 			alpaca_getapiversions( AsyncWebServerRequest * );
		void			alpaca_getdescription( AsyncWebServerRequest * );
		void			alpaca_getconfigureddevices( AsyncWebServerRequest * );
		void 			alpaca_getsetup( AsyncWebServerRequest * );
		void 			dispatch_dome_request( AsyncWebServerRequest * );
		void			dispatch_observingconditions_request( AsyncWebServerRequest * );
		void 			dispatch_request( AsyncWebServerRequest * );
		void			dispatch_safetymonitor_request( AsyncWebServerRequest * );
		void 			dispatch_telescope_request( AsyncWebServerRequest * );
		bool		 	extract_transaction_details( AsyncWebServerRequest *, bool );
		void			does_not_exist( AsyncWebServerRequest * );
		void			get_config( AsyncWebServerRequest * );
		bool			get_configured_devices( char *, size_t );
		void			not_implemented( AsyncWebServerRequest * );
		void			not_implemented( AsyncWebServerRequest *, const char * );
		void			on_packet( AsyncUDPPacket  );
		void			send_file( AsyncWebServerRequest * );
};

#endif
