switux/AstroWeatherStation/src/defaults.h

/*	
  	defaults.h
  	
	(c) 2023-2024 F.Lesage

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
	You should have received a copy of the GNU General Public License along
	with this program. If not, see <https://www.gnu.org/licenses/>.
*/

#pragma once
#ifndef _defaults_H
#define _defaults_H

#include "Embedded_Template_Library.h"
#include "etl/string.h"

const etl::string<128>	DEFAULT_LOCATION					= "Somewhere on Earth";

const uint32_t			DEFAULT_SENSOR_POLLING_MS_INTERVAL	= 15000;

static const uint8_t DEFAULT_AUTOMATIC_UPDATES		= 1;
static const char DEFAULT_SERVER[]				= "www.datamancers.net";
static const char DEFAULT_WIFI_STA_SSID[]		= "AstroWeatherStation";
static const char DEFAULT_WIFI_STA_PASSWORD[]	= "AWS2023!";
static const char DEFAULT_WIFI_AP_SSID[]		= "AstroWeatherStation";
static const char DEFAULT_WIFI_AP_PASSWORD[]	= "AWS2023!";
static const char DEFAULT_TZNAME[]				= "CET-1CEST-2,M3.5.0/02:00:00,M10.5.0/03:00:00";
static const char DEFAULT_URL_PATH[]			= "weather";
static const char DEFAULT_WIFI_STA_IP[]			= "192.168.169.1/24";
static const char DEFAULT_WIFI_STA_GW[]			= "192.168.169.1";
static const char DEFAULT_WIFI_STA_DNS[]		= "8.8.8.8";
static const char DEFAULT_WIFI_AP_IP[]			= "192.168.168.1/24";
static const char DEFAULT_WIFI_AP_GW[]			= "192.168.168.1";
static const char DEFAULT_WIFI_AP_DNS[]			= "8.8.8.8";
static const char DEFAULT_ETH_IP[]				= "192.168.170.1/24";
static const char DEFAULT_ETH_GW[]				= "192.168.170.1";
static const char DEFAULT_ETH_DNS[]				= "8.8.8.8";

// Datamancers.net ROOT CA
static const char  DEFAULT_ROOT_CA[] =
"-----BEGIN CERTIFICATE-----\n"
"MIIFazCCA1OgAwIBAgIRAIIQz7DSQONZRGPgu2OCiwAwDQYJKoZIhvcNAQELBQAw\n"
"TzELMAkGA1UEBhMCVVMxKTAnBgNVBAoTIEludGVybmV0IFNlY3VyaXR5IFJlc2Vh\n"
"cmNoIEdyb3VwMRUwEwYDVQQDEwxJU1JHIFJvb3QgWDEwHhcNMTUwNjA0MTEwNDM4\n"
"WhcNMzUwNjA0MTEwNDM4WjBPMQswCQYDVQQGEwJVUzEpMCcGA1UEChMgSW50ZXJu\n"
"ZXQgU2VjdXJpdHkgUmVzZWFyY2ggR3JvdXAxFTATBgNVBAMTDElTUkcgUm9vdCBY\n"
"MTCCAiIwDQYJKoZIhvcNAQEBBQADggIPADCCAgoCggIBAK3oJHP0FDfzm54rVygc\n"
"h77ct984kIxuPOZXoHj3dcKi/vVqbvYATyjb3miGbESTtrFj/RQSa78f0uoxmyF+\n"
"0TM8ukj13Xnfs7j/EvEhmkvBioZxaUpmZmyPfjxwv60pIgbz5MDmgK7iS4+3mX6U\n"
"A5/TR5d8mUgjU+g4rk8Kb4Mu0UlXjIB0ttov0DiNewNwIRt18jA8+o+u3dpjq+sW\n"
"T8KOEUt+zwvo/7V3LvSye0rgTBIlDHCNAymg4VMk7BPZ7hm/ELNKjD+Jo2FR3qyH\n"
"B5T0Y3HsLuJvW5iB4YlcNHlsdu87kGJ55tukmi8mxdAQ4Q7e2RCOFvu396j3x+UC\n"
"B5iPNgiV5+I3lg02dZ77DnKxHZu8A/lJBdiB3QW0KtZB6awBdpUKD9jf1b0SHzUv\n"
"KBds0pjBqAlkd25HN7rOrFleaJ1/ctaJxQZBKT5ZPt0m9STJEadao0xAH0ahmbWn\n"
"OlFuhjuefXKnEgV4We0+UXgVCwOPjdAvBbI+e0ocS3MFEvzG6uBQE3xDk3SzynTn\n"
"jh8BCNAw1FtxNrQHusEwMFxIt4I7mKZ9YIqioymCzLq9gwQbooMDQaHWBfEbwrbw\n"
"qHyGO0aoSCqI3Haadr8faqU9GY/rOPNk3sgrDQoo//fb4hVC1CLQJ13hef4Y53CI\n"
"rU7m2Ys6xt0nUW7/vGT1M0NPAgMBAAGjQjBAMA4GA1UdDwEB/wQEAwIBBjAPBgNV\n"
"HRMBAf8EBTADAQH/MB0GA1UdDgQWBBR5tFnme7bl5AFzgAiIyBpY9umbbjANBgkq\n"
"hkiG9w0BAQsFAAOCAgEAVR9YqbyyqFDQDLHYGmkgJykIrGF1XIpu+ILlaS/V9lZL\n"
"ubhzEFnTIZd+50xx+7LSYK05qAvqFyFWhfFQDlnrzuBZ6brJFe+GnY+EgPbk6ZGQ\n"
"3BebYhtF8GaV0nxvwuo77x/Py9auJ/GpsMiu/X1+mvoiBOv/2X/qkSsisRcOj/KK\n"
"NFtY2PwByVS5uCbMiogziUwthDyC3+6WVwW6LLv3xLfHTjuCvjHIInNzktHCgKQ5\n"
"ORAzI4JMPJ+GslWYHb4phowim57iaztXOoJwTdwJx4nLCgdNbOhdjsnvzqvHu7Ur\n"
"TkXWStAmzOVyyghqpZXjFaH3pO3JLF+l+/+sKAIuvtd7u+Nxe5AW0wdeRlN8NwdC\n"
"jNPElpzVmbUq4JUagEiuTDkHzsxHpFKVK7q4+63SM1N95R1NbdWhscdCb+ZAJzVc\n"
"oyi3B43njTOQ5yOf+1CceWxG1bQVs5ZufpsMljq4Ui0/1lvh+wjChP4kqKOJ2qxq\n"
"4RgqsahDYVvTH9w7jXbyLeiNdd8XM2w9U/t7y0Ff/9yi0GE44Za4rF2LN9d11TPA\n"
"mRGunUHBcnWEvgJBQl9nJEiU0Zsnvgc/ubhPgXRR4Xq37Z0j4r7g1SgEEzwxA57d\n"
"emyPxgcYxn/eR44/KJ4EBs+lVDR3veyJm+kXQ99b21/+jh5Xos1AnX5iItreGCc=\n"
"-----END CERTIFICATE-----\n";

#endif
